Electro707/PCB-4-In-A-Row/Firmware/Firmware.ino

/**
 *
 * This is an Arduino wrapper file for the 4-in-a-row soldering kit by Electro707
 *
 * This file does nothing, because the Arduino IDE will automatically select `main.c` to
 * compile, which includes the main() function.
 */
